novintic/Fluke-9010A-Pod-Adapters/Fluke Adapter Pics/IMG_5679.jpeg

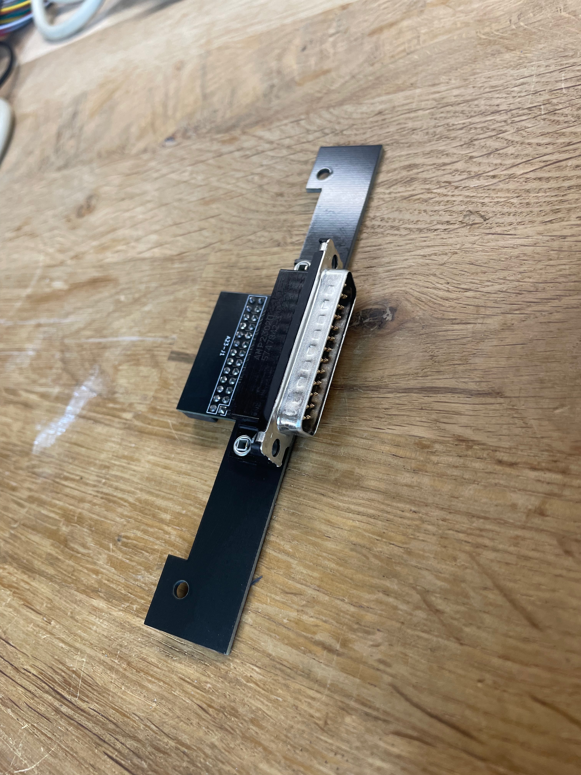
Fluke Adapter Pics/IMG_5679.jpeg
