novintic/Fluke-9010A-Pod-Adapters/Fluke Adapter Pics/IMG_5680.jpeg

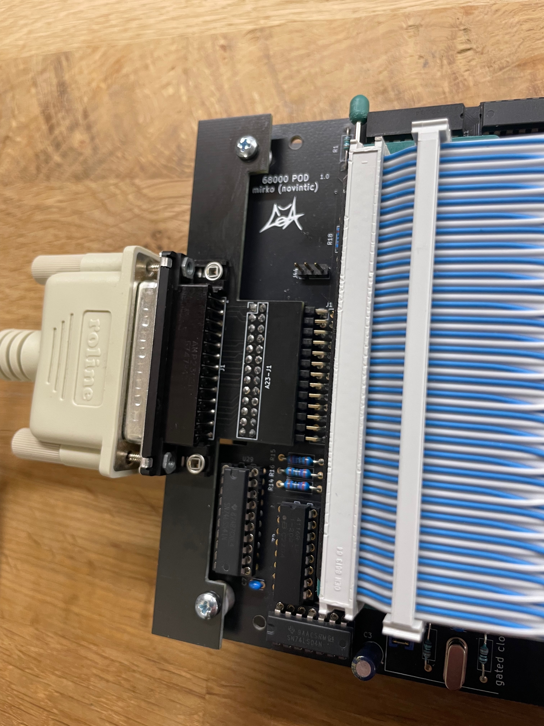
Fluke Adapter Pics/IMG_5680.jpeg
