novintic/Fluke-9010A-Pod-Adapters/Fluke Adapter Pics/IMG_5682.jpeg

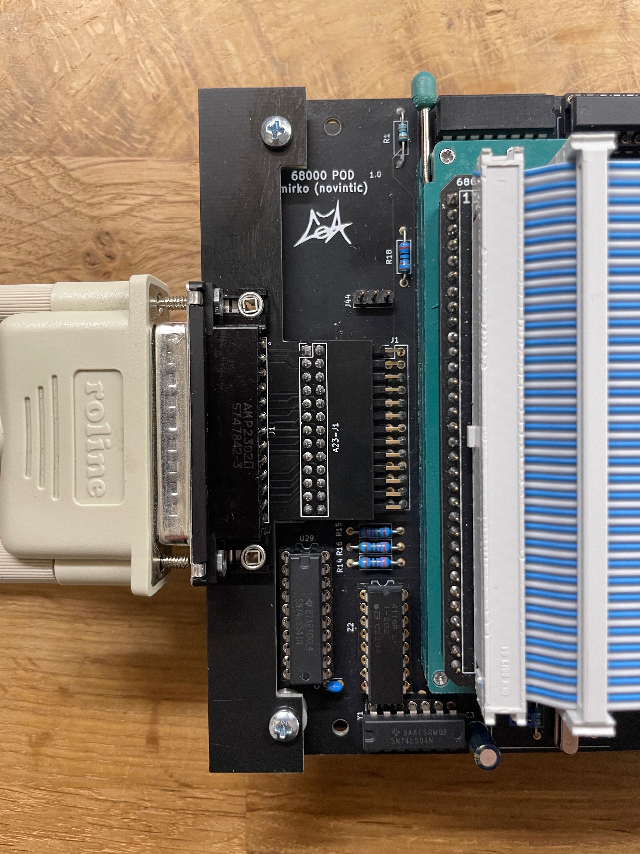
Fluke Adapter Pics/IMG_5682.jpeg
