novintic/Fluke-9010A-Pod-Adapters/Fluke Adapter Pics/IMG_5686.jpeg

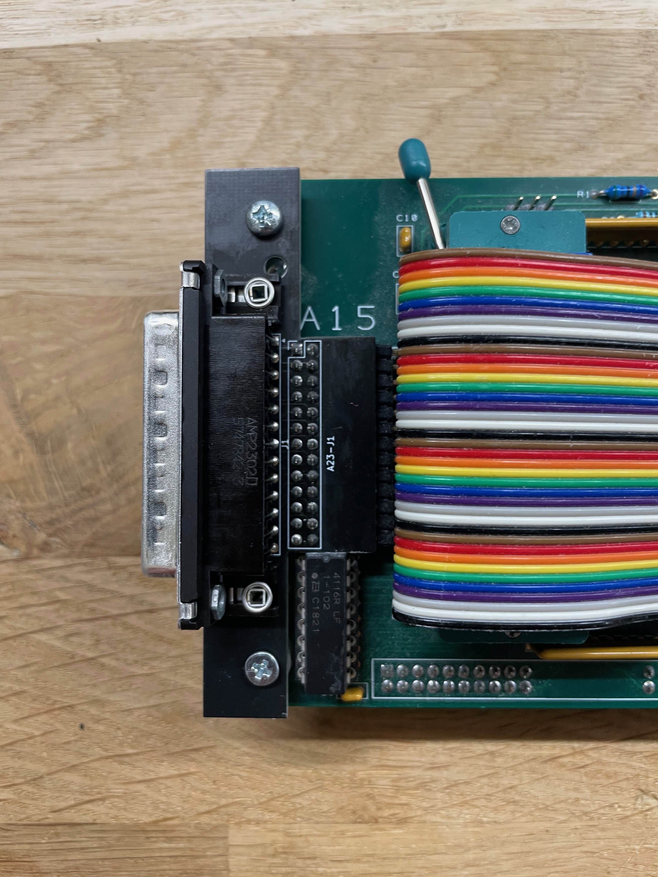
Fluke Adapter Pics/IMG_5686.jpeg
