novintic/Fluke-9010A-Pod-Adapters/Fluke Adapter Pics/IMG_5713.jpeg

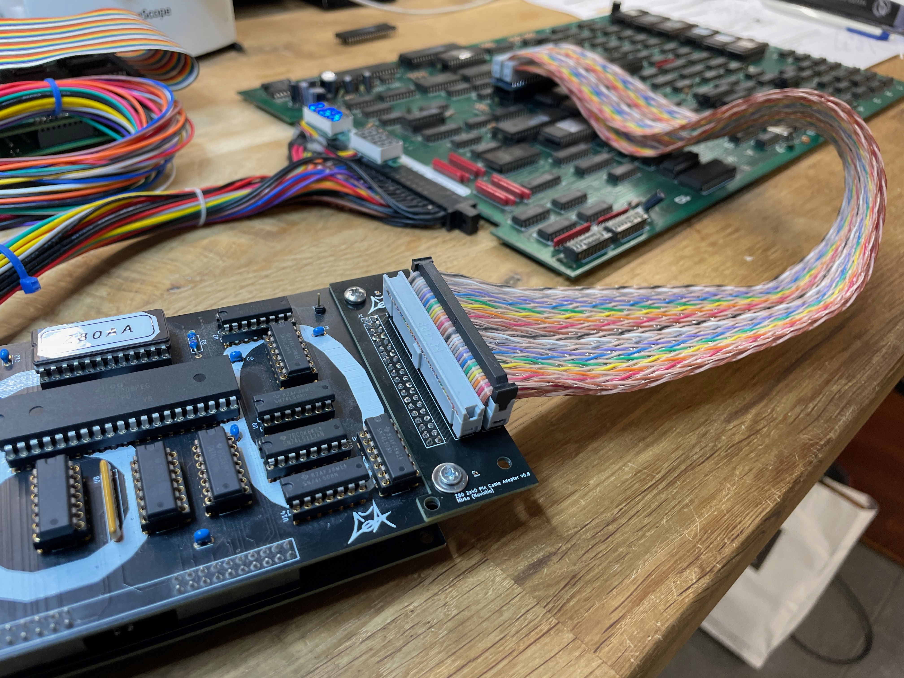
Fluke Adapter Pics/IMG_5713.jpeg
