novintic/Fluke-9010A-Pod-Adapters/Fluke Adapter Pics/IMG_5716.jpeg

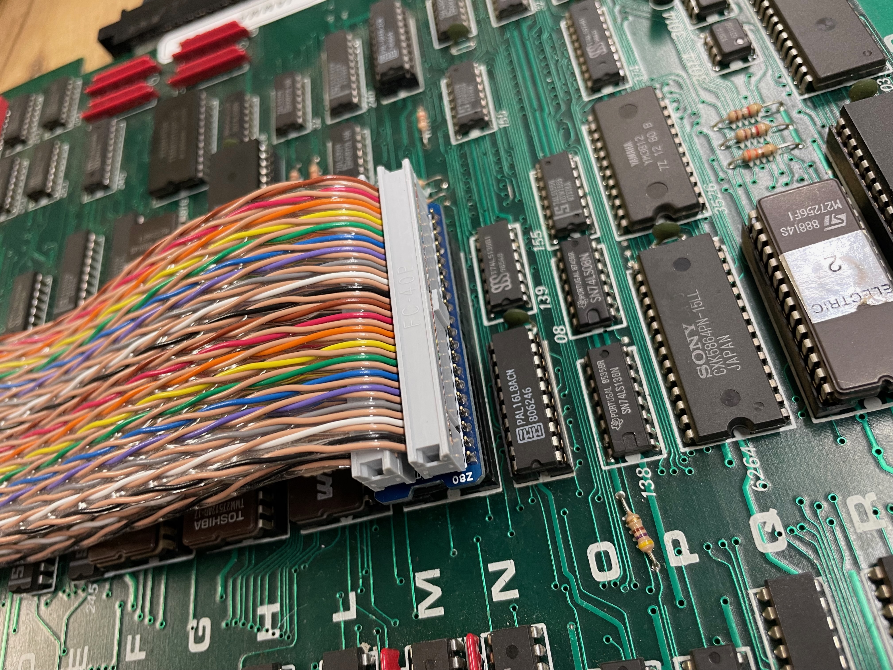
Fluke Adapter Pics/IMG_5716.jpeg
